daviddoo02/strandbeest_robot/STLs/arm c.STL

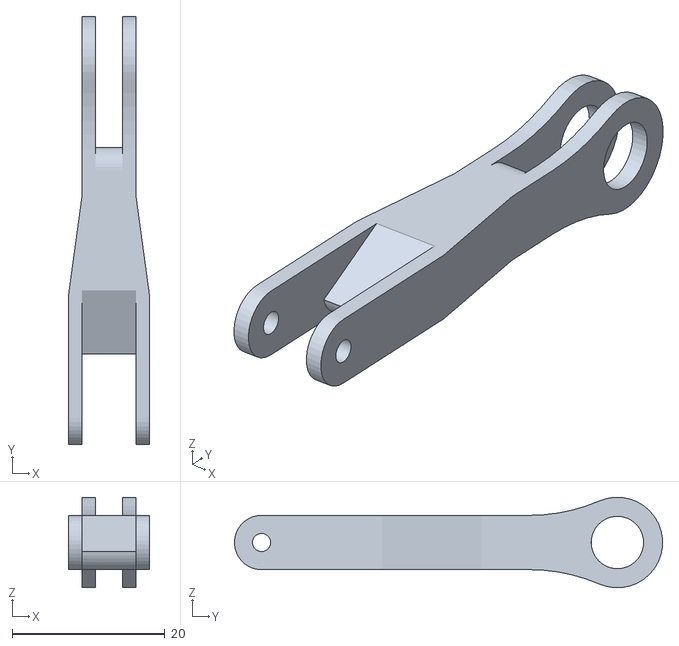
[picture p18: CAD file, 2024-01-17]
STLs/arm c.STL
10.7 x 56.0 x 11.8
