daviddoo02/strandbeest_robot/STLs/Side.STL

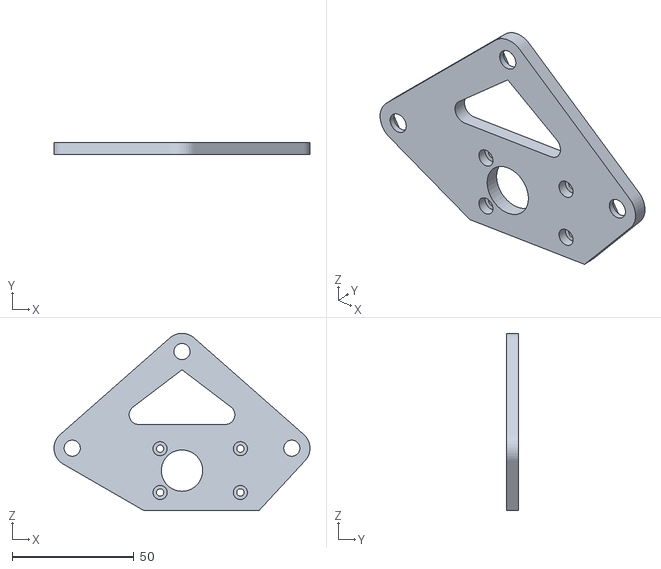
[picture p19: CAD file, 2024-01-17]
STLs/Side.STL
105.2 x 5.00 x 72.9
