daviddoo02/strandbeest_robot/CAD/Middle Crank.SLDASM

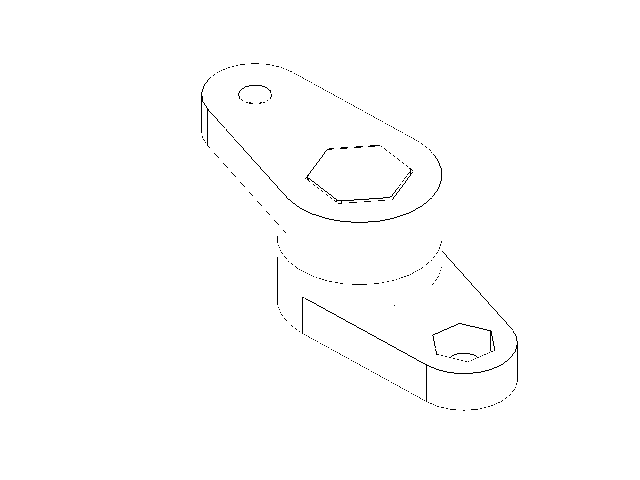
[picture p20: CAD file, 2024-01-17]
CAD/Middle Crank.SLDASM
Middle Crank^Middle Crank x 2
Shaft^Middle Crank
