daviddoo02/strandbeest_robot/CAD/Leg.SLDASM

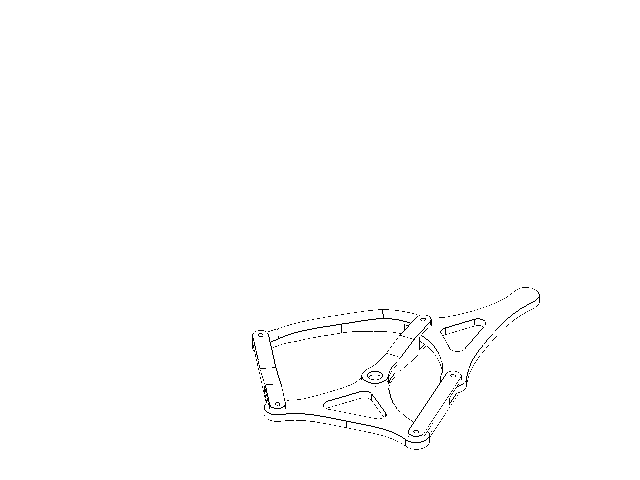
[picture p21: CAD file, 2024-01-17]
CAD/Leg.SLDASM
arm j^Leg
arm k^Leg
bottom triangle^Leg
top triangle^Leg
arm c^Leg
arm f^Leg
